Caleb-Robinson3109/LoComm/src/esp/LoCommBuildPacket.h

/*
This file contianes the functions that build the packets like SACK, SEND, PACK, etc
*/

#ifndef BUILD_PACKET_H
#define BUILD_PACKET_H

#include "LoCommAPI.h"
#include "LoCommLib.h"
#include "globals.h"
#include "security_protocol.h"

#include <stdint.h> //uint8_t, uint32_t, ...
#include <stddef.h> //size_t

#define CACK_SIZE 16
#define PWAK_SIZE 20
#define DCAK_SIZE 16
#define SPAK_SIZE 20
#define SACK_SIZE 18
#define SNAK_SIZE 16
#define EPAK_SIZE 16
#define SCAK_SIZE 48
#define GPAK_SIZE 37

//builds the CACK (send ack) packet
void build_CACK_packet();

//pass word ack
void build_PWAK_packet();

//disconnect ack
void build_DCAK_packet();

//set password ack
void build_SPAK_packet();

//sets the send ack
void build_SACK_packet();

void build_SNAK_packet();

void build_EPAK_packet();

void build_SCAK_packet();

void build_GPAK_packet();

#endif
