Caleb-Robinson3109/LoComm/src/api/api_funcs/LoCommAPISendMessage.py

import serial
import random #for gen random tag
import struct #creation of the packet
import binascii #crc-16 (crc_hqx)
import math
from api_funcs.LoCommContext import LoCommContext
from api_funcs.LoCommDebugPacket import print_packet_debug

def craft_SEND_packet(tag: int, name: str, id: int, text: str, total_packets: int, curr_packet) -> bytes:
    start_bytes: int = 0x1234
    packet_size: int = len(name) + len(text) + 24
    message_type: bytes = b"SEND"
    #total_packets - 2, curr_packet - 2, name len - 1, text len -2, name, text
    message: bytes = struct.pack(f">BHHBH{len(name)}s{len(text)}s", id, total_packets, curr_packet + 1, len(name), len(text), name.encode('ascii'), text.encode('ascii'))

    #computer the payload for the checksum
    payload: bytes = struct.pack(">H", packet_size) + message_type + struct.pack(">I", tag) + message 
    crc: int = binascii.crc_hqx(payload, 0)

    end_bytes: int = 0x5678

    packet: bytes = struct.pack(f">HH4sI{len(message)}sHH",
                                start_bytes, 
                                packet_size,
                                message_type,
                                tag,
                                message,
                                crc,
                                end_bytes)
    return packet

def check_SACK_packet(packet: bytes, tag: int, total_packets: int, packet_num: int) -> tuple[str, bool]:
    start_bytes: int
    packet_size: int
    message_type: bytes
    ret_tag: int
    message: int #we know the message will only contain the chunk number so we set it to int
    crc: int
    end_bytes: int

    start_bytes, packet_size, message_type, ret_tag, message, crc, end_bytes = struct.unpack(">HH4sIHHH", packet)

    if start_bytes != 0x1234:
        return f"start bytes error 0x1234, {start_bytes}", False
    
    if packet_size != 18:
        return f"packet size error 18, {packet_size}", False
    
    if message_type != b"SACK":
        return f"message type error SACK, {message_type}", False
    
    if ret_tag != tag:
        return f"tag mismatch {tag}, {ret_tag}", False
    
    if packet_num + 1 != message:
        return f"packet number error {packet_num}, {message}", False
    
    payload: bytes = struct.pack(">H4sIH", packet_size, message_type, tag, message)
    crc_check: int = binascii.crc_hqx(payload, 0)

    if crc_check != crc:
        return f"crc fail {crc}, {crc_check}", False
    
    if end_bytes != 0x5678:
        return f"end bytes fail 0x5678, {end_bytes}", False
    
    return "no error", True 

def locomm_api_send_message(sender_name: str, reciver_id: int, message: str, ser: serial.Serial, context: LoCommContext) -> bool:
    #split the message into 1000 char chucnks and send each chunk (same tag)
    tag: int = random.randint(0, 0xFFFFFFFF)
    total_packets = math.ceil(len(message) / 1000)
    for i in range (total_packets):
        #for each chucnk also checks if its the last chunk
        chunk: str = message[i * 1000 : (i+1) * 1000] if i != total_packets else message[i * 1000 : len(message)]
        #build packet
        packet: bytes = craft_SEND_packet(tag, sender_name, reciver_id, chunk, total_packets, i)

        #send_recv_packet
        try:
            print_packet_debug(packet, True) 
            ser.write(packet)
            ser.flush()

            #wait for responce 
            while(not context.SACK_flag):
                pass

            print_packet_debug(context.packet, False)
            error_code: str
            send_status: bool
            try:
                error_code, send_status = check_SACK_packet(context.packet, tag, total_packets, i)
            except Exception as e:
                raise ValueError(f"check SACK packet error {e}")
            if(not send_status):
                raise ValueError(f"FAIL send of packet {i+1}/{total_packets} - error: {error_code}")
        except Exception as e:
            print(f"Serial error when sending message: {e}")
            context.SACK_flag = False
            return False
        
        context.SACK_flag = False
    return True
