Caleb-Robinson3109/LoComm/src/esp/globals.cpp

#include "globals.h"

SimpleArraySet<SERIAL_READY_TO_SEND_BUFFER_SIZE, 5> serialReadyToSendArray;

Adafruit_SSD1306 display(SCREEN_WIDTH, SCREEN_HEIGHT, &Wire, OLED_RST);

uint32_t epochAtBoot = 0; 

Preferences storage;

uint8_t device_name[32] = {'d', 'e', 'f', 'a', 'u', 'l', 't', 0x00,
    0x00, 0x00, 0x00, 0x00, 0x00, 0x00, 0x00, 0x00,
    0x00, 0x00, 0x00, 0x00, 0x00, 0x00, 0x00, 0x00,
    0x00, 0x00, 0x00, 0x00, 0x00, 0x00, 0x00, 0x00};

const uint8_t default_password[32] = {'p', 'a', 's', 's', 'w', 'o', 'r', 'd',
    0x00, 0x00, 0x00, 0x00, 0x00, 0x00, 0x00, 0x00,
    0x00, 0x00, 0x00, 0x00, 0x00, 0x00, 0x00, 0x00,
    0x00, 0x00, 0x00, 0x00, 0x00, 0x00, 0x00, 0x00};

uint8_t deviceIDList[32];

uint8_t deviceID = 255;
