Caleb-Robinson3109/LoComm/src/esp/globals.h

#pragma once

#include <Adafruit_SSD1306.h>
#include "functions.h"

//Serial TX Related Variables
//TODO for sake of performance, this should probably be a CyclicArrayList
extern SimpleArraySet<SERIAL_READY_TO_SEND_BUFFER_SIZE, 5> serialReadyToSendArray; //Queue for sending data out to serial //(location in the rxMessageBuffer, size)
extern Adafruit_SSD1306 display;
extern uint32_t epochAtBoot;
extern Preferences storage;
extern uint8_t device_name[32];
extern const uint8_t default_password[32];
extern uint8_t deviceIDList[32];
extern uint8_t deviceID; 
